mferris/StratoScan/enclosure/Retro Radar Enclosure/antenna_mount.stl

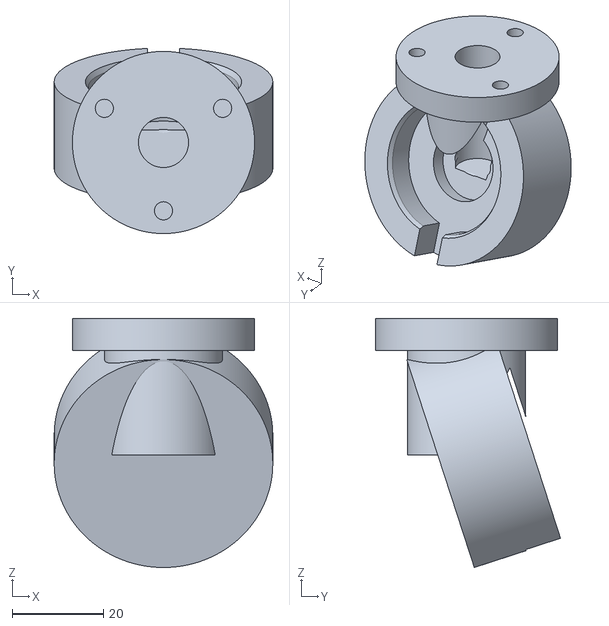
[picture p11: CAD file, 2026-10-07]
enclosure/Retro Radar Enclosure/antenna_mount.stl
48.0 x 40.7 x 54.7
