mferris/StratoScan/enclosure/Kitten Enclosure Two-Tone/antenna_mount_sma.stl

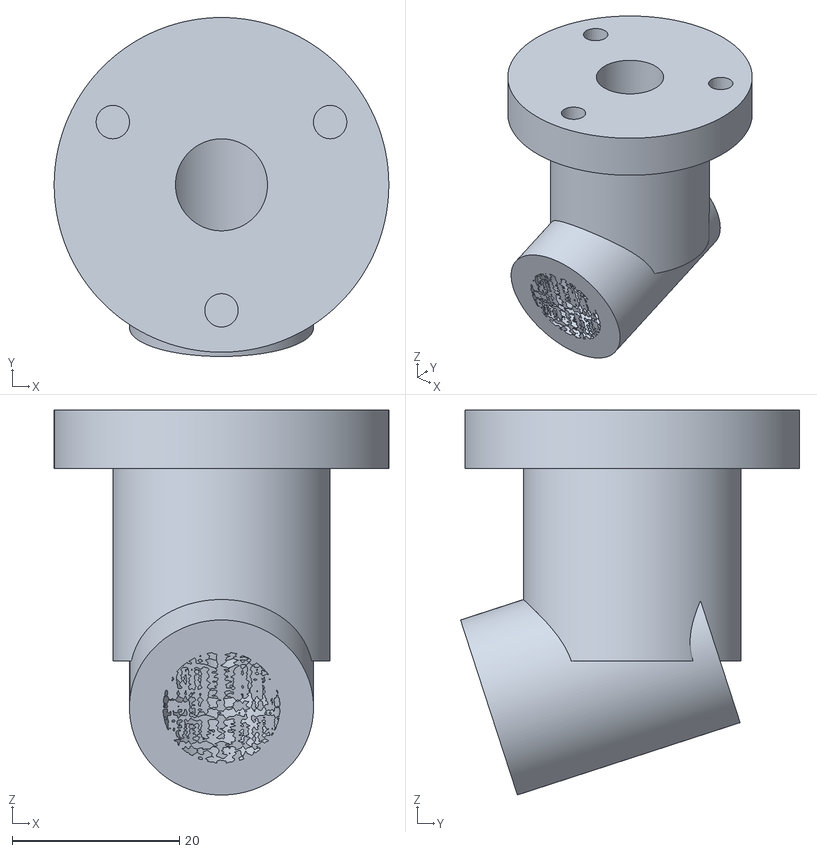
[picture p12: CAD file, 2026-10-07]
enclosure/Kitten Enclosure Two-Tone/antenna_mount_sma.stl
40.0 x 40.5 x 46.0
