mferris/StratoScan/deploy/setupd.py

#!/usr/bin/env python3
"""Root helper for the StratoScan setup server.

This is the privilege boundary. The HTTP server (setup-server.py) runs
unprivileged and cannot touch the system directly; it asks this process to
perform a fixed set of verbs over a unix socket. The HTTP parser is the part
most likely to be attacked and is therefore exactly the part that must not be
root.

Design rules, all of which exist because breaking them strands or exposes the
appliance:

  * Closed verb enum. There is no generic "run nmcli" or "run systemctl"
    passthrough, so a compromised web tier cannot escalate to arbitrary
    commands -- only to the specific, validated operations below.
  * Every parameter is re-validated HERE, not merely in the caller. The web
    tier's validation is a UX convenience; this is the security control.
  * No shell, ever. subprocess with an argv list, absolute paths, a fixed
    minimal environment, and an explicit timeout.
  * Secrets (WiFi PSK, Tailscale auth key) never appear in argv, where any
    local user could read them from /proc, nor in the journal. They are
    passed through 0600 files on tmpfs that are unlinked immediately.
  * Every state write is atomic and fsynced, including the directory entry.
    A power cut mid-write must never leave a half-written config that stops
    the device booting onto the network.
  * Network changes are add-then-switch with an armed rollback. The working
    profile is never edited or deleted; a new candidate profile is created
    with autoconnect off and only promoted once connectivity is proven.
"""
import contextlib
import fcntl
import json
import os
import re
import shutil
import shlex
import socket
import socketserver
import subprocess
import sys
import time

SOCK_PATH = "/run/stratoscan/setupd.sock"
RUN_DIR = "/run/stratoscan"
STATE_DIR = "/var/lib/stratoscan-setup"
PENDING = os.path.join(STATE_DIR, "pending.json")
LOCK = os.path.join(STATE_DIR, "lock")
READSB_DEFAULT = "/etc/default/readsb"
READSB_ORIG = os.path.join(STATE_DIR, "readsb.default.orig")
READSB_BACKUP = os.path.join(STATE_DIR, "readsb.fr-backup")
CONFIG_JSON = "/var/www/html/config.json"
OFFLINE_MAP_DIR = "/var/www/html/offline-map"
OFFLINE_MAP = "/opt/stratoscan/offline-map.py"
AIRPORTS_JSON = "/opt/stratoscan/airports.json"

CANDIDATE_PROFILE = "fr-candidate"
HOTSPOT_PROFILE = "fr-hotspot"
CONFIRM_WINDOW_S = 180

ENV = {"PATH": "/usr/sbin:/usr/bin:/sbin:/bin", "LC_ALL": "C"}
NMCLI = "/usr/bin/nmcli"
TAILSCALE = "/usr/bin/tailscale"
SYSTEMCTL = "/usr/bin/systemctl"

# Continental US. Deliberately not global: the airport table is CONUS-only,
# and a coordinate outside it means the user mistyped rather than that they
# are genuinely in Alaska.
# Global. These were 24..49.5 and -125..-66.5 -- the continental US -- which
# made the device unconfigurable anywhere else on Earth: a receiver in the
# Netherlands (52.16N, 4.49E) was rejected outright as "outside the
# continental US". A gifted unit has no reason to be US-only.
LAT_MIN, LAT_MAX = -90.0, 90.0
LON_MIN, LON_MAX = -180.0, 180.0

RE_TS_HOSTNAME = re.compile(r"^[a-z0-9]([a-z0-9-]{0,30}[a-z0-9])?$")
RE_TS_AUTHKEY = re.compile(r"^tskey-[A-Za-z0-9_-]{10,200}$")
RE_ATC_MOUNT = re.compile(r"^[a-z0-9][a-z0-9_-]{2,39}$")


class Err(Exception):
    def __init__(self, code, detail=""):
        super().__init__(code)
        self.code = code
        self.detail = detail


# ---------------------------------------------------------------- utilities

def run(argv, timeout=30, check=False, input_bytes=None):
    """subprocess with no shell, fixed env, absolute paths and a timeout."""
    try:
        p = subprocess.run(argv, env=ENV, timeout=timeout, capture_output=True,
                           input=input_bytes, shell=False)
    except subprocess.TimeoutExpired:
        raise Err("timeout", argv[0])
    if check and p.returncode != 0:
        raise Err("command_failed", redact(p.stderr.decode("utf-8", "replace"))[:400])
    return p


_SECRETS = []


def redact(text):
    """Strip any known secret from text before it can reach a log."""
    for s in _SECRETS:
        if s:
            text = text.replace(s, "<redacted>")
    return text


def atomic_write(path, data, mode=0o600):
    """Write + fsync the file AND its directory.

    Without the directory fsync a power cut can leave the rename unrecorded,
    which for /etc/default/readsb means the receiver may not start.
    """
    d = os.path.dirname(path)
    os.makedirs(d, exist_ok=True)
    tmp = os.path.join(d, f".{os.path.basename(path)}.tmp")
    with open(tmp, "w") as f:
        f.write(data)
        f.flush()
        os.fsync(f.fileno())
    os.chmod(tmp, mode)
    os.replace(tmp, path)
    dfd = os.open(d, os.O_DIRECTORY)
    try:
        os.fsync(dfd)
    finally:
        os.close(dfd)


@contextlib.contextmanager
def state_lock():
    os.makedirs(STATE_DIR, exist_ok=True)
    with open(LOCK, "w") as f:
        try:
            fcntl.flock(f, fcntl.LOCK_EX | fcntl.LOCK_NB)
        except BlockingIOError:
            raise Err("busy", "another change is in progress")
        try:
            yield
        finally:
            fcntl.flock(f, fcntl.LOCK_UN)


def secret_file(name, value):
    """Hand a secret to a subprocess without putting it in argv."""
    os.makedirs(RUN_DIR, mode=0o700, exist_ok=True)
    path = os.path.join(RUN_DIR, name)
    atomic_write(path, value, mode=0o600)
    return path


# --------------------------------------------------------------- validation

def v_lat(v):
    if isinstance(v, bool) or not isinstance(v, (int, float)):
        raise Err("bad_lat", "not a number")
    if v != v or v in (float("inf"), float("-inf")):
        raise Err("bad_lat", "not finite")
    if not (LAT_MIN <= v <= LAT_MAX):
        raise Err("lat_out_of_range", f"{v} is not a latitude")
    return float(v)


def v_lon(v):
    if isinstance(v, bool) or not isinstance(v, (int, float)):
        raise Err("bad_lon", "not a number")
    if v != v or v in (float("inf"), float("-inf")):
        raise Err("bad_lon", "not finite")
    if not (LON_MIN <= v <= LON_MAX):
        raise Err("lon_out_of_range", f"{v} is not a longitude")
    return float(v)


def v_ssid(v):
    if not isinstance(v, str):
        raise Err("bad_ssid")
    b = v.encode("utf-8")
    if not (1 <= len(b) <= 32):
        raise Err("bad_ssid", "must be 1-32 bytes")
    if any(c in v for c in ("\x00", "\r", "\n")):
        raise Err("bad_ssid", "control characters")
    # nmcli has no reliable "--" terminator across all subcommands, so an
    # SSID that begins with a dash could be read as an option. Rejected
    # rather than risk it; genuinely rare, and documented in the UI.
    if v.startswith("-"):
        raise Err("ssid_leading_dash", "network names starting with '-' are not supported")
    return v


def v_psk(v):
    if v is None or v == "":
        return None
    if not isinstance(v, str):
        raise Err("bad_psk")
    if any(c in v for c in ("\x00", "\r", "\n")):
        raise Err("bad_psk", "control characters")
    # Same reasoning as v_ssid's leading-dash rule, which this was missing:
    # the value is passed to nmcli as an argument, and nmcli has no reliable
    # "--" terminator across subcommands, so a leading dash risks being read
    # as an option. WPA allows it; no real network uses it.
    if v.startswith("-"):
        raise Err("psk_leading_dash",
                  "passwords starting with '-' are not supported")
    if re.fullmatch(r"[0-9a-fA-F]{64}", v):
        return v
    if not (8 <= len(v) <= 63):
        raise Err("bad_psk", "must be 8-63 characters")
    if any(ord(c) < 0x20 or ord(c) > 0x7e for c in v):
        raise Err("bad_psk", "unsupported characters")
    return v


def v_ts_hostname(v):
    if not isinstance(v, str) or not RE_TS_HOSTNAME.match(v):
        raise Err("bad_hostname", "lowercase letters, digits and hyphens only")
    return v


def v_authkey(v):
    if not isinstance(v, str) or not RE_TS_AUTHKEY.match(v):
        raise Err("bad_authkey", "does not look like a Tailscale auth key")
    return v


def v_atc_mount(v):
    if v in (None, ""):
        return ""
    if not isinstance(v, str) or not RE_ATC_MOUNT.match(v):
        raise Err("bad_atc_mount")
    return v


def load_airports():
    with open(AIRPORTS_JSON) as f:
        return {a["code"]: a for a in json.load(f)["airports"]}


# ------------------------------------------------------------------ readsb

def rewrite_readsb_location(lat, lon):
    """Replace --lat/--lon inside DECODER_OPTIONS, preserving everything else.

    /etc/default/readsb is shell-sourced by root, so this is a command
    execution sink: anything injected here runs as root at boot. The file is
    tokenised with shlex, only the lat/lon tokens are substituted, values are
    re-serialised from validated floats (the caller's bytes never reach the
    file), and the result is refused if any token looks like it could break
    out of its quoting.
    """
    with open(READSB_DEFAULT) as f:
        original = f.read()

    if not os.path.exists(READSB_ORIG):
        atomic_write(READSB_ORIG, original, mode=0o600)
    atomic_write(READSB_BACKUP, original, mode=0o600)

    out_lines, touched = [], False
    for line in original.splitlines():
        m = re.match(r'^(\s*DECODER_OPTIONS\s*=\s*)"(.*)"\s*$', line)
        if not m:
            out_lines.append(line)
            continue
        prefix, body = m.group(1), m.group(2)
        toks = shlex.split(body)
        new, i = [], 0
        seen_lat = seen_lon = False
        while i < len(toks):
            t = toks[i]
            if t == "--lat" and i + 1 < len(toks):
                new += ["--lat", f"{lat:.5f}"]; i += 2; seen_lat = True; continue
            if t == "--lon" and i + 1 < len(toks):
                new += ["--lon", f"{lon:.5f}"]; i += 2; seen_lon = True; continue
            if t.startswith("--lat="):
                new.append(f"--lat={lat:.5f}"); i += 1; seen_lat = True; continue
            if t.startswith("--lon="):
                new.append(f"--lon={lon:.5f}"); i += 1; seen_lon = True; continue
            new.append(t); i += 1
        if not seen_lat:
            new += ["--lat", f"{lat:.5f}"]
        if not seen_lon:
            new += ["--lon", f"{lon:.5f}"]
        for t in new:
            if any(c in t for c in ('"', "'", "`", "$", "\\", "\n", "\r")):
                raise Err("readsb_unsafe_token", "refusing to write an unsafe option")
        out_lines.append(f'{prefix}"{" ".join(new)}"')
        touched = True

    if not touched:
        raise Err("readsb_no_decoder_options", "DECODER_OPTIONS line not found")

    atomic_write(READSB_DEFAULT, "\n".join(out_lines) + "\n", mode=0o644)
    os.chown(READSB_DEFAULT, 0, 0)
    return original


def strip_readsb_location(text):
    """`text` (an /etc/default/readsb) with every --lat/--lon option removed.

    Same tokenise-and-reserialise discipline as rewrite_readsb_location: this
    file is shell-sourced by root. readsb runs fine with no position; the
    page then simply has no home to draw a map around until one is set.
    """
    out = []
    for line in text.splitlines():
        m = re.match(r'^(\s*DECODER_OPTIONS\s*=\s*)"(.*)"\s*$', line)
        if not m:
            out.append(line)
            continue
        toks, keep, i = shlex.split(m.group(2)), [], 0
        while i < len(toks):
            t = toks[i]
            if t in ("--lat", "--lon"):
                i += 2
                continue
            if t.startswith(("--lat=", "--lon=")):
                i += 1
                continue
            keep.append(t)
            i += 1
        for t in keep:
            if any(c in t for c in ('"', "'", "`", "$", "\\", "\n", "\r")):
                raise Err("readsb_unsafe_token", "refusing to write an unsafe option")
        out.append(f'{m.group(1)}"{" ".join(keep)}"')
    return "\n".join(out) + "\n"


def restart_readsb_or_rollback(previous):
    """Restart readsb; restore the previous file if it does not come back.

    "active" alone is not proof -- readsb can be running and decoding
    nothing. aircraft.json's mtime must advance too, or the receiver is up
    but deaf, which from the owner's point of view is just as broken.
    """
    run([SYSTEMCTL, "restart", "readsb"], timeout=30)
    aircraft = "/run/readsb/aircraft.json"
    before = os.path.getmtime(aircraft) if os.path.exists(aircraft) else 0
    deadline = time.time() + 20
    ok = False
    while time.time() < deadline:
        time.sleep(1)
        active = run([SYSTEMCTL, "is-active", "readsb"], timeout=10).stdout.strip() == b"active"
        moved = os.path.exists(aircraft) and os.path.getmtime(aircraft) > before
        if active and moved:
            ok = True
            break
    if not ok:
        atomic_write(READSB_DEFAULT, previous, mode=0o644)
        os.chown(READSB_DEFAULT, 0, 0)
        run([SYSTEMCTL, "restart", "readsb"], timeout=30)
        raise Err("readsb_did_not_recover", "reverted to the previous location")
    return True


# -------------------------------------------------------------------- wifi

def nm_active_wifi_uuid():
    p = run([NMCLI, "-t", "-f", "UUID,TYPE,DEVICE", "connection", "show", "--active"])
    for line in p.stdout.decode().splitlines():
        parts = line.split(":")
        if len(parts) >= 3 and parts[1] == "802-11-wireless" and parts[2] == "wlan0":
            return parts[0]
    return None


def net_status():
    """What the device is actually on right now, for display in the UI.

    Shown so the owner can see what is already configured rather than having
    to guess whether a screen has been filled in before.
    """
    ssid = None
    p = run([NMCLI, "-t", "-f", "ACTIVE,SSID", "device", "wifi"], timeout=20)
    for line in p.stdout.decode("utf-8", "replace").splitlines():
        parts = re.split(r"(?<!\\):", line)
        if len(parts) >= 2 and parts[0] == "yes":
            ssid = parts[1].replace("\\:", ":")
            break
    addr = None
    a = run([NMCLI, "-t", "-f", "IP4.ADDRESS", "device", "show", "wlan0"], timeout=15)
    for line in a.stdout.decode().splitlines():
        if "/" in line:
            addr = line.split(":", 1)[-1].split("/")[0]
            break
    # NetworkManager already runs its own connectivity check, so ask it
    # rather than making an outbound request of our own: "full" means the
    # internet is genuinely reachable, "limited"/"portal" means associated
    # but going nowhere (the case a plain IP address cannot distinguish),
    # "none" means no usable network at all. Anything unexpected, including
    # a disabled checker reporting "unknown", is passed through verbatim for
    # the UI to treat as indeterminate rather than as a failure.
    c = run([NMCLI, "-t", "-f", "CONNECTIVITY", "general"], timeout=15)
    conn = c.stdout.decode("utf-8", "replace").strip().splitlines()
    return {"ssid": ssid, "ipv4": addr, "hotspotActive": hotspot_active(),
            "connectivity": conn[0].strip() if conn else "unknown"}


def hotspot_address():
    """The address the hotspot is actually serving on.

    Never hardcode this. NetworkManager's shared mode hands out 10.42.0.1 by
    default, but it is configurable and can differ -- and the first version of
    the setup screen printed a hardcoded 192.168.4.1, which was simply the
    development network's router. Anyone following it reached nothing.
    """
    a = run([NMCLI, "-t", "-f", "IP4.ADDRESS", "device", "show", "wlan0"], timeout=15)
    for line in a.stdout.decode().splitlines():
        if "/" in line:
            return line.split(":", 1)[-1].split("/")[0]
    return None


def nm_delete_profile(name_or_uuid):
    run([NMCLI, "connection", "delete", name_or_uuid], timeout=20)


def wifi_scan():
    run([NMCLI, "device", "wifi", "rescan"], timeout=25)
    time.sleep(2)
    p = run([NMCLI, "-t", "-f", "SSID,SIGNAL,SECURITY,IN-USE", "device", "wifi", "list"], timeout=25)
    seen, out = set(), []
    for line in p.stdout.decode("utf-8", "replace").splitlines():
        # nmcli -t escapes literal colons as \:  -- split on unescaped ones
        parts = re.split(r"(?<!\\):", line)
        if len(parts) < 4:
            continue
        ssid = parts[0].replace("\\:", ":")
        if not ssid or ssid in seen:
            continue
        seen.add(ssid)
        try:
            signal = int(parts[1])
        except ValueError:
            signal = 0
        out.append({"ssid": ssid, "signal": signal,
                    "secured": parts[2] not in ("", "--"),
                    "inUse": parts[3].strip() == "*"})
    out.sort(key=lambda n: -n["signal"])
    return out


def write_pending(rec):
    atomic_write(PENDING, json.dumps(rec), mode=0o660)


def read_pending():
    try:
        with open(PENDING) as f:
            return json.load(f)
    except Exception:
        return None


def clear_pending():
    with contextlib.suppress(FileNotFoundError):
        os.unlink(PENDING)


def connectivity_ok():
    """Activated is not the same as working.

    NetworkManager reports 'activated' for an association that never got a
    DHCP lease, which is a half-brick: the device looks connected and is
    unreachable. Require an address, a default route, and a real response.
    """
    p = run([NMCLI, "-t", "-f", "IP4.ADDRESS", "device", "show", "wlan0"], timeout=10)
    if b"/" not in p.stdout:
        return False, "wifi_no_ip"
    p = run([NMCLI, "-t", "-f", "IP4.GATEWAY", "device", "show", "wlan0"], timeout=10)
    gw = p.stdout.decode().strip().split(":", 1)[-1]
    if not gw:
        return False, "wifi_no_gateway"
    ping = run(["/bin/ping", "-c", "1", "-W", "3", gw], timeout=10)
    if ping.returncode != 0:
        return False, "wifi_gateway_unreachable"
    return True, None


def wifi_connect(ssid, psk, hidden=False):
    """Add a candidate profile and try it, without disturbing the working one.

    The existing profile is never edited or deleted. If anything goes wrong
    -- wrong password, out of range, no DHCP, power cut -- the device still
    has its old network to fall back to, and pending.json (written and
    fsynced BEFORE the first mutation) tells the reconciler to put it back.
    """
    ssid = v_ssid(ssid)
    psk = v_psk(psk)
    _SECRETS.append(psk or "")

    known_good = nm_active_wifi_uuid()
    write_pending({
        "kind": "wifi",
        "startedAt": time.time(),
        "deadline": time.time() + CONFIRM_WINDOW_S,
        "knownGoodUuid": known_good,
        "candidate": CANDIDATE_PROFILE,
        "ssid": ssid,
    })

    with contextlib.suppress(Exception):
        nm_delete_profile(CANDIDATE_PROFILE)

    argv = [NMCLI, "connection", "add", "type", "wifi", "con-name", CANDIDATE_PROFILE,
            "ifname", "wlan0", "ssid", ssid,
            "connection.autoconnect", "no"]
    if hidden:
        argv += ["wifi.hidden", "yes"]
    run(argv, timeout=20, check=True)

    if psk:
        # NOTE: the PSK *is* in argv for the second call below, and is
        # readable from /proc/<pid>/cmdline for as long as that nmcli runs.
        #
        # This comment used to claim the opposite -- "the key never appears in
        # argv" -- describing a protection the code did not implement. That is
        # worse than no comment: it is the same failure as the X-FR-Public
        # marker, a defence that exists only in prose. secret_file() is real
        # and is used for the Tailscale auth key (see tailscale_up); it is
        # NOT usable here, because nmcli takes property values only as
        # arguments, with no file or stdin form.
        #
        # Left as-is deliberately. Closing it means writing the secret into
        # the keyfile under /etc/NetworkManager/system-connections (already
        # 0600 root:root) and reloading, which cannot be rehearsed on a
        # remote device whose only link is the WiFi being reconfigured: a
        # mistake there strands the unit with no way back in. The exposure it
        # would buy back is narrow -- a local process running as some other
        # service user, sampling /proc during a sub-second window, to learn
        # the WiFi password of the network it is already attached to.
        run([NMCLI, "connection", "modify", CANDIDATE_PROFILE,
             "wifi-sec.key-mgmt", "wpa-psk"], timeout=20, check=True)
        run([NMCLI, "connection", "modify", CANDIDATE_PROFILE,
             "wifi-sec.psk", psk], timeout=20, check=True)

    up = run([NMCLI, "connection", "up", CANDIDATE_PROFILE], timeout=60)
    if up.returncode != 0:
        err = redact(up.stderr.decode("utf-8", "replace")).lower()
        reason = ("wifi_auth_failed" if "secrets" in err or "password" in err
                  else "wifi_ssid_not_found" if "not found" in err or "no network" in err
                  else "wifi_failed")
        wifi_rollback()
        raise Err(reason, "")

    ok, why = connectivity_ok()
    if not ok:
        wifi_rollback()
        raise Err(why, "")

    return {"state": "awaiting_confirm", "ssid": ssid,
            "confirmDeadline": time.time() + CONFIRM_WINDOW_S}


def wifi_confirm():
    """Promote the candidate only once someone has proved they can still reach
    the device on the new network."""
    pend = read_pending()
    if not pend or pend.get("kind") != "wifi":
        raise Err("nothing_pending")
    run([NMCLI, "connection", "modify", CANDIDATE_PROFILE,
         "connection.autoconnect", "yes"], timeout=20)
    run([NMCLI, "connection", "modify", CANDIDATE_PROFILE,
         "connection.id", f"fr-{pend['ssid'][:24]}"], timeout=20)
    clear_pending()
    return {"state": "ok", "ssid": pend.get("ssid")}


def wifi_rollback():
    """Undo an unconfirmed change. Must never itself throw."""
    pend = read_pending()
    with contextlib.suppress(Exception):
        nm_delete_profile(CANDIDATE_PROFILE)
    if pend and pend.get("knownGoodUuid"):
        with contextlib.suppress(Exception):
            run([NMCLI, "connection", "up", pend["knownGoodUuid"]], timeout=45)
    clear_pending()
    ok = False
    with contextlib.suppress(Exception):
        ok, _ = connectivity_ok()
    if not ok:
        # Last resort: make the device reachable by its own hotspot rather
        # than leaving it dark. This is the path that turns "unrecoverable
        # brick" into "join StratoScan-Setup from a phone".
        with contextlib.suppress(Exception):
            hotspot_start()
    return {"rolledBack": True, "connectivity": ok}


def hotspot_start():
    run([NMCLI, "connection", "delete", HOTSPOT_PROFILE], timeout=20)
    psk = hotspot_psk()
    run([NMCLI, "device", "wifi", "hotspot", "ifname", "wlan0",
         "con-name", HOTSPOT_PROFILE, "ssid", "StratoScan-Setup",
         "password", psk], timeout=45)
    return {"ssid": "StratoScan-Setup", "psk": psk}


def hotspot_psk():
    """Stable per-device PSK, so the label/on-screen value stays valid."""
    path = os.path.join(STATE_DIR, "hotspot-psk")
    try:
        with open(path) as f:
            return f.read().strip()
    except FileNotFoundError:
        import secrets as _s
        psk = "".join(_s.choice("23456789abcdefghjkmnpqrstuvwxyz") for _ in range(10))
        atomic_write(path, psk, mode=0o660)
        return psk


def hotspot_active():
    """Whether the AP is actually up right now, not merely configured.

    The onboarding screen branches on this: telling a recipient to join
    'StratoScan-Setup' when the device is already on their WiFi sends them
    looking for a network that does not exist.
    """
    p = run([NMCLI, "-t", "-f", "NAME", "connection", "show", "--active"], timeout=15)
    return HOTSPOT_PROFILE in p.stdout.decode("utf-8", "replace")


def hotspot_stop():
    with contextlib.suppress(Exception):
        nm_delete_profile(HOTSPOT_PROFILE)
    return {"stopped": True}


# --------------------------------------------------------- location/airport


# ---- Locale: timezone and WiFi regulatory domain ---------------------------
# Both were baked into the image (America/New_York, wifi country US). A unit
# gifted abroad showed the wrong clock on every timestamp and ran its radio on
# the wrong channel set, and neither was reachable from the setup page.
TZ_RE = re.compile(r"\A[A-Za-z][A-Za-z0-9+_-]*(?:/[A-Za-z0-9+_-]+){0,2}\Z")
COUNTRY_RE = re.compile(r"\A[A-Z]{2}\Z")


def v_timezone(v):
    if not isinstance(v, str) or not TZ_RE.match(v):
        raise Err("bad_timezone", "not a timezone name")
    # Must be one systemd actually knows: this string reaches timedatectl.
    if v not in list_timezones():
        raise Err("unknown_timezone", f"{v} is not a known timezone")
    return v


def v_country(v):
    if not isinstance(v, str) or not COUNTRY_RE.match(v.upper()):
        raise Err("bad_country", "not a 2-letter country code")
    return v.upper()


def list_timezones():
    # run() returns BYTES. Forgetting that produced a list of b"..." here and
    # a dict of bytes in get_locale(), which json.dumps cannot serialise -- so
    # the handler raised while building its reply and the caller saw an empty
    # response with nothing in the journal to explain it.
    out = run(["timedatectl", "list-timezones"], timeout=15)
    text = out.stdout.decode("utf-8", "replace") if isinstance(out.stdout, bytes) else out.stdout
    return [ln.strip() for ln in text.splitlines() if ln.strip()]


def timezones_for_country(cc):
    """Zones tzdata associates with a country, from zone.tab."""
    cc = (cc or "").upper()
    zones = []
    try:
        with open("/usr/share/zoneinfo/zone.tab") as f:
            for line in f:
                if line.startswith("#"):
                    continue
                parts = line.split("\t")
                if len(parts) >= 3 and parts[0].strip().upper() == cc:
                    zones.append(parts[2].strip())
    except OSError:
        pass
    return zones


def _text(out):
    v = getattr(out, "stdout", b"") or b""
    return v.decode("utf-8", "replace") if isinstance(v, bytes) else v


def get_locale():
    tz = run(["timedatectl", "show", "-p", "Timezone", "--value"], timeout=10)
    country = ""
    try:
        country = _text(run(["raspi-config", "nonint", "get_wifi_country"],
                            timeout=15)).strip().upper()
    except Exception:
        country = ""
    return {"timezone": _text(tz).strip(), "wifiCountry": country}


def set_timezone(tz):
    tz = v_timezone(tz)
    run(["timedatectl", "set-timezone", tz], timeout=20, check=True)
    return {"timezone": tz}


def set_wifi_country(cc):
    """Set the WiFi regulatory country. Takes effect on the next boot.

    raspi-config is the right tool -- it writes cfg80211.ieee80211_regdom into
    the kernel command line, which is what actually survives -- but two things
    about it matter here, both found by running it on the device:

    1. IT EXITS NON-ZERO ON SUCCESS. Its NetworkManager/wpa_cli steps try to
       reach a session message bus, which does not exist when this runs from a
       daemon, so it prints "Failed to open connection to session message bus"
       and returns 1 having already written the setting. check=True would
       report failure for a change that worked, so the result is judged by
       READING THE VALUE BACK instead of by the exit code.

    2. THE RUNNING REGULATORY DOMAIN DOES NOT CHANGE. The Pi's Broadcom radio
       registers a custom regulatory table (phy#0 reports country 99), so the
       driver overrides `iw reg set` and the global domain reads 98 rather
       than the country asked for. Only a reboot applies it. Saying "done"
       here without saying that would be a lie the recipient discovers later,
       so the caller is told.
    """
    cc = v_country(cc)
    # What it was, so the caller can tell a real change from a no-op and only
    # ask for a restart when one is actually needed. Setting NL over NL should
    # not send anyone to power-cycle a working device.
    before = _text(run(["raspi-config", "nonint", "get_wifi_country"],
                       timeout=20)).strip().upper()
    run(["raspi-config", "nonint", "do_wifi_country", cc], timeout=45)
    stored = _text(run(["raspi-config", "nonint", "get_wifi_country"],
                       timeout=20)).strip().upper()
    if stored != cc:
        raise Err("wifi_country_failed", f"asked for {cc}, device reports {stored}")
    changed = before != cc
    return {"wifiCountry": cc, "previous": before,
            "changed": changed,
            # Only true when it will actually differ after the restart.
            "appliesAfterReboot": changed}



# ---- Address lookup --------------------------------------------------------
# Typing coordinates is the reliable way in and the unfriendly one. This turns
# an address into a position using OpenStreetMap's Nominatim.
#
# Done HERE, on the device, not in the browser: during first-time setup the
# phone is joined to this device's own hotspot, which has no route to the
# internet, while the Pi has already been put on WiFi in the previous step.
# A browser-side lookup would simply fail at exactly the moment it is needed.
#
# The address is the owner's home, so it is worth being precise about where it
# goes: the query string reaches Nominatim and nothing else, it is not logged
# here, and the coordinates it returns stay on the device the same way typed
# ones do. Entering coordinates by hand remains available for anyone who would
# rather not send an address anywhere.
NOMINATIM = "https://nominatim.openstreetmap.org/search"
GEOCODE_UA = "StratoScan-kiosk/1.0 (+https://github.com/mferris/StratoScan)"


def v_query(v):
    if not isinstance(v, str):
        raise Err("bad_query", "not a string")
    q = v.strip()
    if not (3 <= len(q) <= 200):
        raise Err("bad_query", "between 3 and 200 characters")
    return q


def geocode(query):
    import json as _json
    import urllib.parse
    import urllib.request
    q = v_query(query)
    url = NOMINATIM + "?" + urllib.parse.urlencode({
        "q": q, "format": "jsonv2", "limit": "6", "addressdetails": "1",
    })
    req = urllib.request.Request(url, headers={"User-Agent": GEOCODE_UA})
    try:
        with urllib.request.urlopen(req, timeout=20) as r:
            # Cap the read: this is untrusted remote input parsed as root.
            raw = r.read(400_000)
    except Exception as e:
        raise Err("geocode_unreachable", type(e).__name__)
    try:
        rows = _json.loads(raw.decode("utf-8", "replace"))
    except ValueError:
        raise Err("geocode_bad_reply", "not JSON")
    out = []
    for row in rows if isinstance(rows, list) else []:
        try:
            lat = float(row["lat"]); lon = float(row["lon"])
        except (KeyError, TypeError, ValueError):
            continue
        if not (-90 <= lat <= 90 and -180 <= lon <= 180):
            continue
        cc = ((row.get("address") or {}).get("country_code") or "").upper()
        out.append({
            "label": str(row.get("display_name", ""))[:180],
            "lat": round(lat, 6), "lon": round(lon, 6),
            "country": cc,
        })
    return {"results": out, "query": q}



# ---- Over-the-air updates --------------------------------------------------
# setupd only shells out to ota.py; the verification, the monotonic serial and
# the rollback all live there. This keeps the privileged surface small: three
# verbs that take no arguments at all, so there is nothing here for a caller to
# steer.
OTA = "/opt/stratoscan/ota.py"


def ota_status():
    r = run([OTA, "status"], timeout=30)
    try:
        return json.loads(_text(r).strip() or "{}")
    except ValueError:
        return {"state": "unknown"}


def ota_check():
    run([OTA, "check"], timeout=120)
    return ota_status()


def ota_apply():
    """Start an update and return immediately.

    This cannot be synchronous. Applying restarts the kiosk, and on the
    touchscreen the kiosk IS the page that asked for the update -- so a
    blocking call would be killed halfway by the thing it started, leaving the
    device mid-update with nobody watching. It also takes up to two minutes,
    because it waits to see whether the new build paints.

    So it runs as a transient unit, outside this process's control group and
    outside the kiosk's. The caller polls ota_status() instead; ota.py writes
    every state transition to status.json as it goes.
    """
    if ota_status().get("state") == "applying":
        raise Err("ota_busy", "an update is already running")
    run(["systemd-run", "--quiet", "--collect",
         "--unit", "stratoscan-ota-apply",
         "--property=Type=oneshot",
         OTA, "apply"], timeout=30, check=True)
    return {"state": "applying", "started": True}


# ---- Health reports (opt-in) ------------------------------------------------
# heartbeat.py owns the key, the report and the sending; setupd only turns it
# on and off for the setup page. A closed pair of verbs whose only parameter
# is a strict boolean -- nothing here for a caller to steer.
HEARTBEAT = "/opt/stratoscan/heartbeat.py"


def _heartbeat():
    import importlib.util
    if not os.path.exists(HEARTBEAT):
        return None
    spec = importlib.util.spec_from_file_location("heartbeat", HEARTBEAT)
    mod = importlib.util.module_from_spec(spec)
    spec.loader.exec_module(mod)
    return mod


EVENTS = "/opt/stratoscan/events.py"


def _events():
    import importlib.util
    if not os.path.exists(EVENTS):
        return None
    spec = importlib.util.spec_from_file_location("events", EVENTS)
    mod = importlib.util.module_from_spec(spec)
    spec.loader.exec_module(mod)
    return mod


def health_status():
    hb = _heartbeat()
    if hb is None:
        return {"available": False}
    key = hb.load_key(create=False)
    return {"available": True, "enabled": hb.enabled(),
            "relayConfigured": bool(hb.RELAY_URL),
            "unit": hb.unit_id(key)[:10] if key else None,
            "last": hb._json(hb.LAST) or None}


def fleet_status():
    hb = _heartbeat()
    if hb is None:
        return {"available": False}
    f = hb.fleet()
    return {"available": True, "fleet": {"name": f.get("name")} if f else None}


def _fleet_call(fn, *args):
    hb = _heartbeat()
    if hb is None:
        raise Err("unavailable", "health reporting is not installed")
    try:
        return getattr(hb, fn)(*args)
    except ValueError as e:
        raise Err("fleet", str(e))


def fleet_join(code):
    if not isinstance(code, str) or not re.match(r"^[A-Za-z0-9 -]{12,20}$", code):
        raise Err("bad_code", "That doesn't look like an invite code.")
    return _fleet_call("fleet_join", code)


def set_health_report(enabled):
    if not isinstance(enabled, bool):
        raise Err("bad_enabled", "enabled must be true or false")
    hb = _heartbeat()
    if hb is None:
        raise Err("unavailable", "health reporting is not installed")
    hb.set_enabled(enabled)
    return health_status()


# ---- The receivers' switches (2026-10-10) ----------------------------------
# The owner can turn the 1090 MHz and 978 MHz radios on and off from the
# radar's own settings screen. The switches are a file radio-select.py reads
# before readsb and the 978 decoder start; changing one restarts the two so
# it takes effect at once. Both are on unless switched off. The power
# safeguard (net-watchdog.py) may pause the 978 decoder on its own; that is
# reported, and switching 978 on again clears the pause.
RADIOS_FILE = "/etc/stratoscan/radios.json"
UAT_UNIT = "stratoscan-uat.service"
UAT_PAUSED = "/run/stratoscan-net/uat-paused"
RADIO_SELECT = "/opt/stratoscan/radio-select.py"


def _radio_switches():
    out = {"1090": True, "978": True}
    try:
        with open(RADIOS_FILE) as f:
            d = json.load(f)
        for k in out:
            if isinstance(d.get(k), bool):
                out[k] = d[k]
    except (OSError, ValueError, AttributeError):
        pass
    return out


def _unit_word(verb, unit):
    try:
        return run([SYSTEMCTL, verb, unit], timeout=15).stdout.decode().strip()
    except Exception:
        return "unknown"


def radios_status():
    """What each switch says and what is actually running."""
    on = _radio_switches()
    products = []
    try:
        import ctypes
        lib = ctypes.CDLL("librtlsdr.so.0")
        for i in range(lib.rtlsdr_get_device_count()):
            bufs = [ctypes.create_string_buffer(256) for _ in range(3)]
            if lib.rtlsdr_get_device_usb_strings(i, *bufs) == 0:
                products.append(bufs[1].value.decode("utf-8", "replace"))
    except Exception:
        pass
    uat_present = any("uat" in p.lower() or "978" in p for p in products)
    return {
        "1090": {"on": on["1090"], "running": _unit_word("is-active", "readsb") == "active"},
        "978": {"on": on["978"], "present": uat_present,
                "installed": _unit_word("is-enabled", UAT_UNIT) in ("enabled", "disabled"),
                "running": _unit_word("is-active", UAT_UNIT) == "active",
                "paused": on["978"] and os.path.exists(UAT_PAUSED)},
    }


def set_radios(params):
    """Switch the 1090 and/or 978 radio on or off: {"1090": bool, "978": bool}."""
    on = _radio_switches()
    changed = False
    for k in ("1090", "978"):
        if k in params:
            if not isinstance(params[k], bool):
                raise Err("bad_switch", f"{k} must be true or false")
            changed |= on[k] != params[k]
            on[k] = params[k]
    if not changed:
        return radios_status()
    os.makedirs(os.path.dirname(RADIOS_FILE), exist_ok=True)
    atomic_write(RADIOS_FILE, json.dumps(on) + "\n", mode=0o644)
    if on["978"]:
        try:
            os.unlink(UAT_PAUSED)    # switching it on again clears the safeguard's pause
        except OSError:
            pass
    # The 978 decoder first, so readsb's restart finds its feed as it should be.
    run([SYSTEMCTL, "restart" if on["978"] else "stop", UAT_UNIT], timeout=60)
    run([SYSTEMCTL, "restart", "readsb"], timeout=60)
    return radios_status()


# ---- Phone pairing (roadmap 2.3) ------------------------------------------
# pairing.py does the work, signing with the unit key; setupd exposes it to
# the radar's own screen (setup-server's loopback-only onboarding listener)
# and to the password-protected setup page. The only parameter anywhere is a
# phone id, checked against the exact shape of one.
PAIRING = "/opt/stratoscan/pairing.py"
RE_PHONE_ID = re.compile(r"^[A-Za-z0-9_-]{43}$")


def _pairing():
    import importlib.util
    if not os.path.exists(PAIRING):
        return None
    spec = importlib.util.spec_from_file_location("pairing", PAIRING)
    mod = importlib.util.module_from_spec(spec)
    spec.loader.exec_module(mod)
    return mod


def _pairing_call(fn_name, *args):
    p = _pairing()
    if p is None:
        raise Err("unavailable", "phone pairing is not installed")
    try:
        return getattr(p, fn_name)(*args)
    except p.RelayError as e:
        raise Err("relay", str(e))


def pair_status():
    if _pairing() is None:
        return {"available": False}
    return {"available": True, **_pairing_call("status")}


def pair_start():
    return _pairing_call("start")


def pair_offer_hash(h):
    if not isinstance(h, str) or not re.match(r"^[0-9a-f]{64}$", h):
        raise Err("bad_hash", "not a SHA-256")
    return _pairing_call("offer_hash", h)


def unit_id():
    return _pairing_call("unit")


def pair_cancel():
    return _pairing_call("cancel")


def pair_remove(phone):
    if not isinstance(phone, str) or not RE_PHONE_ID.match(phone):
        raise Err("bad_phone", "not a phone id")
    return _pairing_call("remove", phone)


# ---- Opt-in feeding (FlightAware) ------------------------------------------
# feeding.py does the work; setupd exposes a closed pair of verbs whose only
# parameter is a strict boolean. Installing takes a minute or two, so turning
# it on runs as a transient unit (like ota_apply) and the page polls status.
FEEDING = "/opt/stratoscan/feeding.py"


def feeding_status():
    if not os.path.exists(FEEDING):
        return {"available": False}
    r = run(["/usr/bin/python3", FEEDING, "status"], timeout=30)
    try:
        st = json.loads(_text(r) or "{}")
    except ValueError:
        st = {}
    st["available"] = True
    return st


def set_feeding(flightaware):
    if not isinstance(flightaware, bool):
        raise Err("bad_enabled", "flightaware must be true or false")
    if not os.path.exists(FEEDING):
        raise Err("unavailable", "feeding is not installed on this unit")
    if flightaware:
        run([SYSTEMCTL, "stop", "stratoscan-feeding.service"], timeout=30)
        run(["systemd-run", "--quiet", "--collect", "--unit", "stratoscan-feeding",
             "--property=Type=oneshot", "/usr/bin/python3", FEEDING, "enable-flightaware"],
            timeout=30, check=True)
    else:
        run(["/usr/bin/python3", FEEDING, "disable-flightaware"], timeout=90)
    return feeding_status()


def set_location(lat, lon):
    # Null Island. A real receiver is never at exactly 0,0, and accepting it
    # silently centres the radar in the Gulf of Guinea with no clue why.
    if v_lat(lat) == 0.0 and v_lon(lon) == 0.0:
        raise Err("lat_out_of_range", "0,0 looks like an unset location")
    lat, lon = v_lat(lat), v_lon(lon)
    previous = rewrite_readsb_location(lat, lon)
    restart_readsb_or_rollback(previous)
    return {"lat": round(lat, 5), "lon": round(lon, 5), "readsbRestarted": True,
            "offlineMap": start_offline_map_build(lat, lon)}


def start_offline_map_build(lat, lon):
    """Fetch the offline fallback map for this location, in the background.

    A minute or so of downloads, so never inline: the setup page is waiting on
    this call. A transient unit, like ota_apply, so it survives this daemon
    restarting and a second location change cannot run two builds at once --
    systemd-run refuses a unit name that is already active. If it fails (no
    internet yet on a unit being set up on the hotspot), net-watchdog's
    periodic check notices the map does not match the location and retries.
    """
    if not os.path.exists(OFFLINE_MAP):
        return False
    # The location change has already succeeded by the time this runs; the
    # map is a nice-to-have that net-watchdog retries, so nothing here may
    # turn a good location change into a reported failure.
    try:
        # A build still running for the PREVIOUS location is now building the
        # wrong area; stop it so this one can take the unit name.
        run([SYSTEMCTL, "stop", "stratoscan-offline-map.service"], timeout=30)
        r = run(["systemd-run", "--quiet", "--collect",
                 "--unit", "stratoscan-offline-map",
                 "--property=Type=oneshot", "--property=Nice=10",
                 "/usr/bin/python3", OFFLINE_MAP, "build", f"{lat:.5f}", f"{lon:.5f}"],
                timeout=30)
        return r.returncode == 0
    except Exception:
        return False


def set_airport(code, atc_mount=""):
    """Write the web app's /config.json from the bundled table.

    Coordinates come from the table, never from the request: the client picks
    a code, not a position. And this file deliberately carries only the
    AIRPORT -- never the receiver's own coordinates, which are the owner's
    home address and reach the app solely via receiver.json, which the funnel
    gateway rounds before it leaves the network.
    """
    airports = load_airports()
    if not isinstance(code, str) or code not in airports:
        raise Err("unknown_airport", str(code)[:16])
    a = airports[code]
    cfg = {"airport": {
        "code": a["code"], "lat": a["lat"], "lon": a["lon"],
        "elevFt": a["elevFt"], "atcMount": v_atc_mount(atc_mount),
        # Carried so the time-zone step can offer that country's zones
        # instead of all 485, and so the WiFi region follows automatically.
        "country": a.get("country", ""),
    }}
    atomic_write(CONFIG_JSON, json.dumps(cfg, indent=1) + "\n", mode=0o644)
    os.chown(CONFIG_JSON, 0, 0)
    return cfg["airport"]


# --------------------------------------------------------------- tailscale

def tailscale_status():
    p = run([TAILSCALE, "status", "--json"], timeout=20)
    if p.returncode != 0:
        return {"state": "unavailable"}
    try:
        d = json.loads(p.stdout)
    except Exception:
        return {"state": "unavailable"}
    self_ = d.get("Self") or {}
    name = (self_.get("DNSName") or "").rstrip(".")
    # Whether a PUBLIC page is actually being served, not merely whether the
    # node is on the tailnet. Without this the UI cannot tell "connected" from
    # "connected and published", and offers to publish something that already
    # is -- which is how it read before this was added.
    funnel_on = False
    sp = run([TAILSCALE, "serve", "status", "--json"], timeout=20)
    if sp.returncode == 0:
        try:
            cfg = json.loads(sp.stdout or b"{}")
            funnel_on = any(bool(v) for v in (cfg.get("AllowFunnel") or {}).values())
        except Exception:
            funnel_on = False
    if not funnel_on:
        # Cross-check: serve status can report AllowFunnel null while funnel
        # status still shows it live, depending on how it was configured.
        fp = run([TAILSCALE, "funnel", "status"], timeout=20)
        if fp.returncode == 0 and b"Funnel on" in fp.stdout:
            funnel_on = True
    return {
        "state": d.get("BackendState", "unknown"),
        "hostname": self_.get("HostName"),
        "magicDnsName": name,
        "funnel": funnel_on,
        "publicUrl": f"https://{name}" if (funnel_on and name) else None,
    }


def tailscale_up(authkey, hostname, enable_funnel=False):
    authkey = v_authkey(authkey)
    hostname = v_ts_hostname(hostname)
    _SECRETS.append(authkey)
    keyfile = secret_file("authkey", authkey)
    try:
        p = run([TAILSCALE, "up", f"--auth-key=file:{keyfile}",
                 f"--hostname={hostname}", "--accept-dns=false"], timeout=90)
        if p.returncode != 0:
            raise Err("tailscale_up_failed",
                      redact(p.stderr.decode("utf-8", "replace"))[:300])
    finally:
        with contextlib.suppress(FileNotFoundError):
            os.unlink(keyfile)

    result = tailscale_status()
    # A rename invalidates any existing serve/funnel config, so re-apply it
    # whenever the node was already publishing. Without this the owner ends up
    # with a device that reports itself connected and a public URL that 404s
    # at DNS, with nothing obviously wrong in either place.
    if enable_funnel or result.get("funnel"):
        result["funnel"] = tailscale_funnel(True)
    return result


# Interactive login, so nobody has to type a 50-character auth key on an
# on-screen keyboard. `tailscale up` without a key prints a short login URL
# and blocks; we capture that URL, leave the process running, and let the
# owner open it on a phone. The device polls until the backend goes Running.
_login_proc = {"p": None, "url": None, "started": 0.0}


def tailscale_login_start(hostname):
    hostname = v_ts_hostname(hostname)
    # A login already in flight: hand back the same URL rather than starting
    # a second one, which would invalidate the first.
    if _login_proc["p"] and _login_proc["p"].poll() is None and _login_proc["url"]:
        return {"url": _login_proc["url"], "state": tailscale_status().get("state")}

    with contextlib.suppress(Exception):
        if _login_proc["p"]:
            _login_proc["p"].terminate()

    proc = subprocess.Popen(
        [TAILSCALE, "up", f"--hostname={hostname}", "--accept-dns=false",
         "--force-reauth"],
        env=ENV, stdout=subprocess.PIPE, stderr=subprocess.STDOUT, shell=False)
    _login_proc.update({"p": proc, "url": None, "started": time.time()})

    # Read only until the URL appears; the process keeps running afterwards,
    # waiting for the owner to complete the login in a browser.
    deadline = time.time() + 30
    url = None
    while time.time() < deadline and proc.poll() is None:
        line = proc.stdout.readline()
        if not line:
            break
        text = line.decode("utf-8", "replace")
        m = re.search(r"https://login\.tailscale\.com/\S+", text)
        if m:
            url = m.group(0).rstrip(".,)")
            break
    if not url:
        # Already logged in: `up` returns immediately with no URL.
        st = tailscale_status()
        if st.get("state") == "Running":
            return {"url": None, "state": "Running", "alreadyLoggedIn": True}
        raise Err("tailscale_no_url", "could not start a login")
    _login_proc["url"] = url
    return {"url": url, "state": tailscale_status().get("state")}


def tailscale_login_status():
    st = tailscale_status()
    running = st.get("state") == "Running"
    if running and _login_proc["p"] and _login_proc["p"].poll() is None:
        with contextlib.suppress(Exception):
            _login_proc["p"].terminate()   # login finished; stop waiting
    return {"state": st.get("state"), "hostname": st.get("hostname"),
            "magicDnsName": st.get("magicDnsName"),
            "url": None if running else _login_proc["url"]}


def tailscale_funnel(enabled):
    """Only ever point Funnel at the filtering gateway, never at lighttpd.

    Pointing it at :80 would publish /setup and the receiver's unrounded
    coordinates straight to the internet. The probe below is a hard gate:
    if the gateway is not actually refusing /setup and /wake right now,
    Funnel is not turned on.
    """
    if enabled:
        for path in ("/setup", "/wake", "/./wake", "/%77ake", "/x/../setup"):
            p = run(["/usr/bin/curl", "-s", "-o", "/dev/null", "-w", "%{http_code}",
                     "--path-as-is", "-X", "POST", "-H", "Content-Length: 0",
                     f"http://127.0.0.1:8085{path}"], timeout=15)
            if p.stdout.strip() != b"404":
                raise Err("funnel_guard_failed",
                          f"gateway did not refuse {path} (got {p.stdout.decode()})")
        # Clear any existing serve config first. Renaming the node (which
        # setting a hostname during setup does) leaves the old config bound to
        # the PREVIOUS name -- serve status then shows a hostname the device no
        # longer has, funnel is off, and the public URL simply does not exist.
        # Observed exactly that on the first unit, both times its node was
        # renamed (the second time on 2026-09-30, to stratoscan-rdu).
        # Tailscale 1.5x changed this CLI. The old `funnel <port> on` form now
        # exits with "the CLI for serve and funnel has changed" -- and because
        # nothing checked that exit code, the device reported success while
        # quietly staying tailnet-only. `funnel --bg <target>` sets up serve
        # and funnel together.
        run([TAILSCALE, "serve", "reset"], timeout=30)
        p = run([TAILSCALE, "funnel", "--bg", "http://127.0.0.1:8085"], timeout=60)
        if p.returncode != 0:
            raise Err("funnel_failed",
                      redact(p.stderr.decode("utf-8", "replace") or
                             p.stdout.decode("utf-8", "replace"))[:300])
    else:
        run([TAILSCALE, "funnel", "reset"], timeout=45)
    st = tailscale_status()
    return {"enabled": st.get("funnel", bool(enabled)),
            "publicUrl": st.get("publicUrl")}


# ------------------------------------------------------------------- reset

def reset_settings():
    """Undo configuration, keep the device on the network.

    Deliberately survivable remotely: it clears what the owner chose, but
    leaves WiFi and Tailscale alone so the device is still reachable
    afterwards. If this dropped the network it would be indistinguishable
    from a brick to anyone without a keyboard.
    """
    with contextlib.suppress(FileNotFoundError):
        os.unlink(CONFIG_JSON)
    if os.path.exists(READSB_ORIG):
        with open(READSB_ORIG) as f:
            pristine = f.read()
        atomic_write(READSB_DEFAULT, pristine, mode=0o644)
        os.chown(READSB_DEFAULT, 0, 0)
        run([SYSTEMCTL, "restart", "readsb"], timeout=30)
    return {"reset": "settings"}


def reset_full():
    """Prepare the unit to be given to someone else.

    Everything below is either a credential or is geolocated to the current
    owner's house, so a unit handed on with any of it still present is a
    privacy problem, not merely untidy:

      * WiFi profiles      -- their network name and password
      * Tailscale state    -- their tailnet identity
      * admin password     -- the new owner must be able to claim it
      * receiver lat/lon   -- their home address, to five decimal places
      * sighting counts    -- which aircraft have passed over their house
      * approach heatmap   -- accumulated tracks around their home airport

    The device is left UNCLAIMED with a fresh claim code, and the hotspot is
    raised so the next owner can reach it with no network of their own. The
    reachability pieces -- hotspot, watchdog, setup service -- are never
    removed, or the unit would arrive dead.
    """
    # 1. network identity
    p = run([NMCLI, "-t", "-f", "UUID,TYPE", "connection", "show"], timeout=20)
    for line in p.stdout.decode("utf-8", "replace").splitlines():
        parts = line.split(":")
        if len(parts) >= 2 and parts[1] == "802-11-wireless":
            with contextlib.suppress(Exception):
                nm_delete_profile(parts[0])

    # 2. tailscale
    with contextlib.suppress(Exception):
        run([TAILSCALE, "funnel", "443", "off"], timeout=30)
    with contextlib.suppress(Exception):
        run([TAILSCALE, "logout"], timeout=60)

    # 3. owner-specific data. The stores are geolocated to their house.
    # The sighting and network stores keep their data in memory and write it
    # back on a timer and on shutdown, so deleting the file under a running
    # store erases nothing: its next flush puts the old owner's history
    # straight back. Stop first (the stop's own flush lands BEFORE the
    # delete), delete, then start them empty.
    stores = ("stratoscan-sighting-store.service",
              "stratoscan-network.service",
              "stratoscan-approach-store.service")
    with contextlib.suppress(Exception):
        run([SYSTEMCTL, "stop", *stores], timeout=60)
    for path in (os.path.join(STATE_DIR, "setup.json"),
                 CONFIG_JSON,
                 "/var/lib/stratoscan-sightings/sightings.json",
                 "/var/lib/stratoscan-approaches/approaches.json",
                 "/var/lib/stratoscan-network/coverage.json"):
        with contextlib.suppress(Exception):
            os.unlink(path)
    with contextlib.suppress(Exception):
        run([SYSTEMCTL, "start", *stores], timeout=60)

    # 4. receiver position: gone, not "back to the shipped default". The
    # saved original only exists if the location was ever set through setup
    # (a unit located by hand -- like the first one -- has none, and used to
    # skip this step and keep its owner's coordinates), and even when it does
    # exist it can carry whoever built the unit's own position. So whatever
    # is restored is stripped of --lat/--lon outright.
    with contextlib.suppress(Exception):
        source = READSB_ORIG if os.path.exists(READSB_ORIG) else READSB_DEFAULT
        with open(source) as f:
            atomic_write(READSB_DEFAULT, strip_readsb_location(f.read()), mode=0o644)
        os.chown(READSB_DEFAULT, 0, 0)
    # Restarted, not just rewritten: until readsb restarts it keeps
    # publishing the old position in receiver.json -- which the page, the
    # public Funnel and net-watchdog's offline-map check all read.
    with contextlib.suppress(Exception):
        run([SYSTEMCTL, "restart", "readsb"], timeout=30)

    # 4a0. feeding: stop, and forget the feeder id -- it is claimed by the
    # previous owner's FlightAware account.
    with contextlib.suppress(Exception):
        if os.path.exists(FEEDING):
            run(["/usr/bin/python3", FEEDING, "reset"], timeout=120)

    # 4a. health reports were agreed to by the previous owner, not this one.
    with contextlib.suppress(Exception):
        hb = _heartbeat()
        if hb:
            hb.set_enabled(False)

    # 4a1. phones paired with this unit are the previous owner's. Unpair
    # them, and retire the unit's identity so that even if the relay could
    # not be reached just now, nothing this unit sends can reach them again.
    with contextlib.suppress(Exception):
        pr = _pairing()
        if pr:
            pr.forget_everything()
    with contextlib.suppress(Exception):
        ev = _events()
        if ev:
            ev.set_enabled(False)

    # 4b. the offline map is an extract of the area around their house. Only
    # after readsb stops reporting that house: net-watchdog rebuilds a missing
    # map for whatever receiver.json says, and deleting it earlier let it come
    # straight back for the old owner's area. A build already in flight is
    # stopped first -- it would otherwise rename a fresh copy back into place
    # after the delete -- and its half-written staging dir goes too.
    with contextlib.suppress(Exception):
        run([SYSTEMCTL, "stop", "stratoscan-offline-map.service"], timeout=30)
    for d in (OFFLINE_MAP_DIR, OFFLINE_MAP_DIR + ".new", OFFLINE_MAP_DIR + ".old"):
        with contextlib.suppress(Exception):
            shutil.rmtree(d)

    clear_pending()

    # 5. a fresh claim code. Without this the device is unclaimABLE after a
    # reset: ensure_claim_code() only ran at daemon startup, and the previous
    # code was deleted when the unit was first claimed -- so the setup screen
    # said "enter the code below" with nothing below it.
    code = None
    with contextlib.suppress(Exception):
        code = ensure_claim_code()

    # 6. leave it reachable and claimable by its next owner
    hs = None
    with contextlib.suppress(Exception):
        hs = hotspot_start()
    return {"reset": "full", "hotspot": (hs or {}).get("ssid", "StratoScan-Setup"),
            "claimCode": code}


# ------------------------------------------------------------------- verbs

VERBS = {
    "wifi_scan": lambda p: wifi_scan(),
    "wifi_connect": lambda p: wifi_connect(p.get("ssid"), p.get("psk"), bool(p.get("hidden"))),
    "wifi_confirm": lambda p: wifi_confirm(),
    "wifi_rollback": lambda p: wifi_rollback(),
    "hotspot_start": lambda p: hotspot_start(),
    "hotspot_stop": lambda p: hotspot_stop(),
    "hotspot_info": lambda p: {"ssid": "StratoScan-Setup", "psk": hotspot_psk(),
                               "active": hotspot_active(),
                               "address": hotspot_address()},
    "set_location": lambda p: set_location(p.get("lat"), p.get("lon")),
    "geocode": lambda p: geocode(p.get("query")),
    "ota_status": lambda p: ota_status(),
    "ota_check": lambda p: ota_check(),
    "ota_apply": lambda p: ota_apply(),
    "get_locale": lambda p: get_locale(),
    "list_timezones": lambda p: {"timezones": list_timezones(),
                                 "forCountry": timezones_for_country(p.get("country", ""))},
    "set_timezone": lambda p: set_timezone(p.get("timezone")),
    "set_wifi_country": lambda p: set_wifi_country(p.get("country")),
    "set_airport": lambda p: set_airport(p.get("code"), p.get("atcMount", "")),
    "tailscale_status": lambda p: tailscale_status(),
    "tailscale_login_start": lambda p: tailscale_login_start(p.get("hostname")),
    "tailscale_login_status": lambda p: tailscale_login_status(),
    "tailscale_up": lambda p: tailscale_up(p.get("authKey"), p.get("hostname"),
                                           bool(p.get("enableFunnel"))),
    "tailscale_funnel": lambda p: tailscale_funnel(bool(p.get("enabled"))),
    "reboot": lambda p: (run([SYSTEMCTL, "reboot"], timeout=10), {"rebooting": True})[1],
    "pending": lambda p: read_pending(),
    "net_status": lambda p: net_status(),
    "reset_settings": lambda p: reset_settings(),
    "reset_full": lambda p: reset_full(),
    "health_status": lambda p: health_status(),
    "set_health_report": lambda p: set_health_report(p.get("enabled")),
    "pair_status": lambda p: pair_status(),
    "pair_start": lambda p: pair_start(),
    "pair_cancel": lambda p: pair_cancel(),
    "pair_offer_hash": lambda p: pair_offer_hash(p.get("hash")),
    "fleet_status": lambda p: fleet_status(),
    "fleet_join": lambda p: fleet_join(p.get("code")),
    "fleet_leave": lambda p: _fleet_call("fleet_leave"),
    "unit_id": lambda p: unit_id(),
    "pair_remove": lambda p: pair_remove(p.get("phone")),
    "feeding_status": lambda p: feeding_status(),
    "set_feeding": lambda p: set_feeding(p.get("flightaware")),
    "radios_status": lambda p: radios_status(),
    "set_radios": lambda p: set_radios(p),
}
# Shutdown is deliberately absent: a remote caller must never be able to
# power off an appliance that then needs a physical visit to turn back on.

MUTATING = {"wifi_connect", "wifi_confirm", "wifi_rollback", "hotspot_start",
            "hotspot_stop", "set_location", "set_airport", "tailscale_up",
            # Only the two that change state. get_locale, list_timezones and
            # geocode are reads, and geocode in particular does up to 20s of
            # network I/O -- holding the state lock across that would block
            # WiFi operations behind an address lookup.
            "set_timezone", "set_wifi_country", "ota_apply",
            "tailscale_funnel", "reboot", "reset_settings", "reset_full",
            "tailscale_login_start", "set_health_report", "set_feeding",
            "pair_start", "pair_cancel", "pair_remove", "pair_offer_hash",
            "fleet_join", "fleet_leave", "set_radios"}


class Handler(socketserver.StreamRequestHandler):
    timeout = 180

    def handle(self):
        try:
            raw = self.rfile.readline(65536)
            req = json.loads(raw or b"{}")
            verb = req.get("verb")
            params = req.get("params") or {}
            if verb not in VERBS:
                raise Err("unknown_verb", str(verb)[:40])
            if verb in MUTATING:
                with state_lock():
                    result = VERBS[verb](params)
            else:
                result = VERBS[verb](params)
            self.reply({"ok": True, "result": result})
        except Err as e:
            self.reply({"ok": False, "code": e.code, "detail": redact(e.detail)})
        except Exception as e:
            self.reply({"ok": False, "code": "internal",
                        "detail": redact(str(e))[:200]})

    def reply(self, obj):
        with contextlib.suppress(Exception):
            self.wfile.write((json.dumps(obj) + "\n").encode())


def resolve_gid():
    """Group shared with the unprivileged web tier, so it alone can reach us."""
    import grp
    name = os.environ.get("SETUP_GROUP", "scsetup")
    try:
        return grp.getgrnam(name).gr_gid
    except KeyError:
        return 0


class Server(socketserver.ThreadingUnixStreamServer):
    daemon_threads = True
    allow_reuse_address = True


def ensure_claim_code():
    """Regenerate the code that authorises first-time setup.

    Written on every start, so an unclaimed device that has been power-cycled
    gets a fresh one. It is deliberately NOT served over HTTP: behind
    lighttpd's proxy every request looks like it came from 127.0.0.1, so a
    "localhost only" route would have been readable by the whole LAN. It goes
    to a file that the on-screen display reads, which makes claiming require
    physical sight of the unit rather than merely being on the network.

    Skipped once the device is claimed, so the code cannot be used to take
    over a device that already has an owner.
    """
    import secrets as _s
    try:
        with open(os.path.join(STATE_DIR, "setup.json")) as f:
            if json.load(f).get("claimed"):
                # already owned -- no code, so it cannot be re-claimed
                with contextlib.suppress(FileNotFoundError):
                    os.unlink(os.path.join(RUN_DIR, "claim-code"))
                return None
    except Exception:
        pass  # unreadable state => treat as unclaimed, never as locked out
    # Crockford-style alphabet: no I/L/O/U, so nothing is misread off a screen
    alphabet = "0123456789ABCDEFGHJKMNPQRSTVWXYZ"
    code = "".join(_s.choice(alphabet) for _ in range(8))
    atomic_write(os.path.join(RUN_DIR, "claim-code"), code, mode=0o640)
    return code


def share_state_dir():
    """Let the unprivileged web tier reach the shared state.

    Both units declare StateDirectory=stratoscan-setup. systemd creates it
    for whichever starts first -- this one, as root -- giving 0700 root:root,
    which locks the web tier out of its OWN state file. The symptom is
    brutal and silent: load_state() fails, the device reports itself
    unclaimed, and the owner is asked to set a password they already set,
    while their real password stops working.

    Shared by group instead. The web tier legitimately reads and writes this
    file (claiming, password changes), so group write is the intent, not a
    weakening of it.
    """
    gid = resolve_gid()
    if not gid:
        return
    with contextlib.suppress(Exception):
        os.chown(STATE_DIR, 0, gid)
        os.chmod(STATE_DIR, 0o2770)   # setgid: new files inherit the group
    for name in os.listdir(STATE_DIR):
        path = os.path.join(STATE_DIR, name)
        with contextlib.suppress(Exception):
            if os.path.isfile(path):
                os.chown(path, os.stat(path).st_uid, gid)
                os.chmod(path, 0o660)


def main():
    os.makedirs(RUN_DIR, mode=0o700, exist_ok=True)
    os.makedirs(STATE_DIR, mode=0o700, exist_ok=True)
    share_state_dir()
    code = ensure_claim_code()
    if code:
        # Also to the journal: on a headless or screen-dead unit this is the
        # only way an owner with shell access can complete setup.
        print(f"setupd: device is UNCLAIMED, setup code is {code}", flush=True)
    with contextlib.suppress(FileNotFoundError):
        os.unlink(SOCK_PATH)
    srv = Server(SOCK_PATH, Handler)
    # 0660 + the web tier's group: the unprivileged HTTP process may talk to
    # us, nothing else on the box may.
    os.chmod(SOCK_PATH, 0o660)
    gid = resolve_gid()
    if gid:
        os.chown(SOCK_PATH, 0, gid)
        os.chown(os.path.join(RUN_DIR, "claim-code"), 0, gid) if os.path.exists(
            os.path.join(RUN_DIR, "claim-code")) else None
        with contextlib.suppress(Exception):
            os.chmod(RUN_DIR, 0o750)
            os.chown(RUN_DIR, 0, gid)
    srv.serve_forever()


if __name__ == "__main__":
    main()
